roboryman/prototroller/models/enclosure.stl

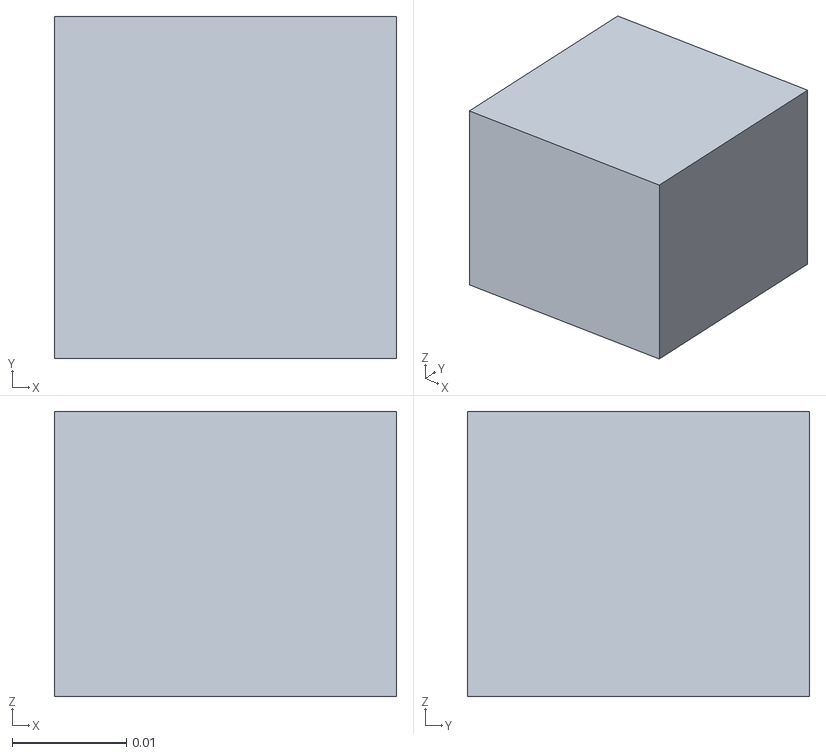
[picture p41: CAD file, 2023-02-21]
models/enclosure.stl
0.03 x 0.03 x 0.025
