roboryman/prototroller/models/Chassis_Top_v1.stl

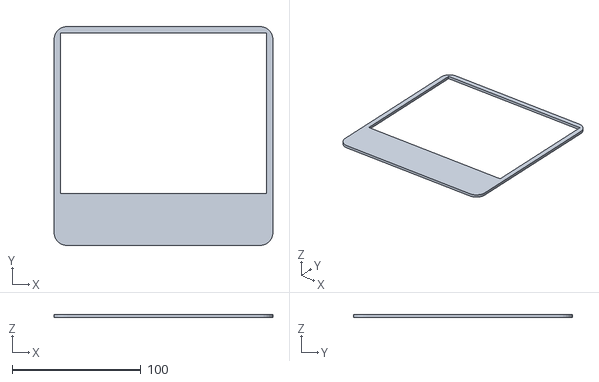
[picture p42: CAD file, 2023-04-07, an earlier design]
models/Chassis_Top_v1.stl
170.0 x 170.0 x 2.50
